DEAD10C5/badge-2017-bsidesindy/image/bsin.jpg

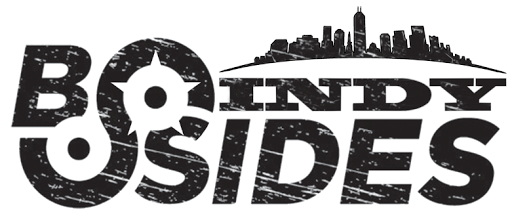
image/bsin.jpg
