DEAD10C5/badge-2017-bsidesindy/image/cleaver2.jpg

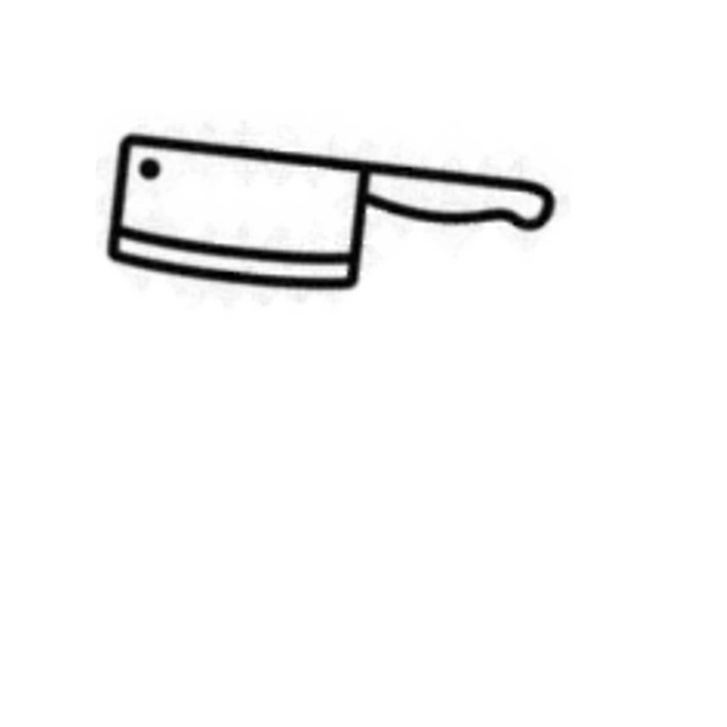
image/cleaver2.jpg
