DEAD10C5/badge-2017-bsidesindy/image/Screenshot-1 Board - -home-thedevilsvoice-eagle-tsrt-untitled.brd-EAGLE 7.5.0 Light.png

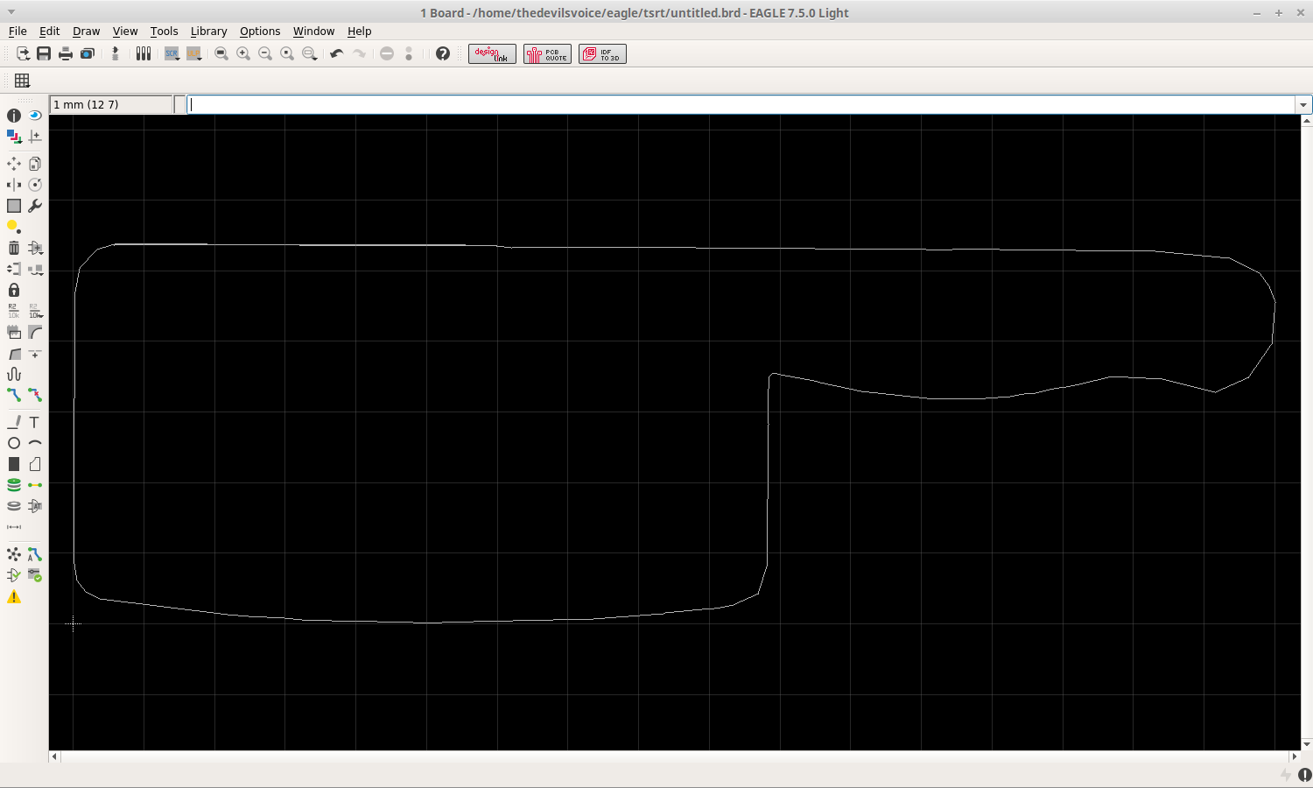
image/Screenshot-1 Board - -home-thedevilsvoice-eagle-tsrt-untitled.brd-EAGLE 7.5.0 Light.png
