DEAD10C5/badge-2017-bsidesindy/image/Screenshot-3.png

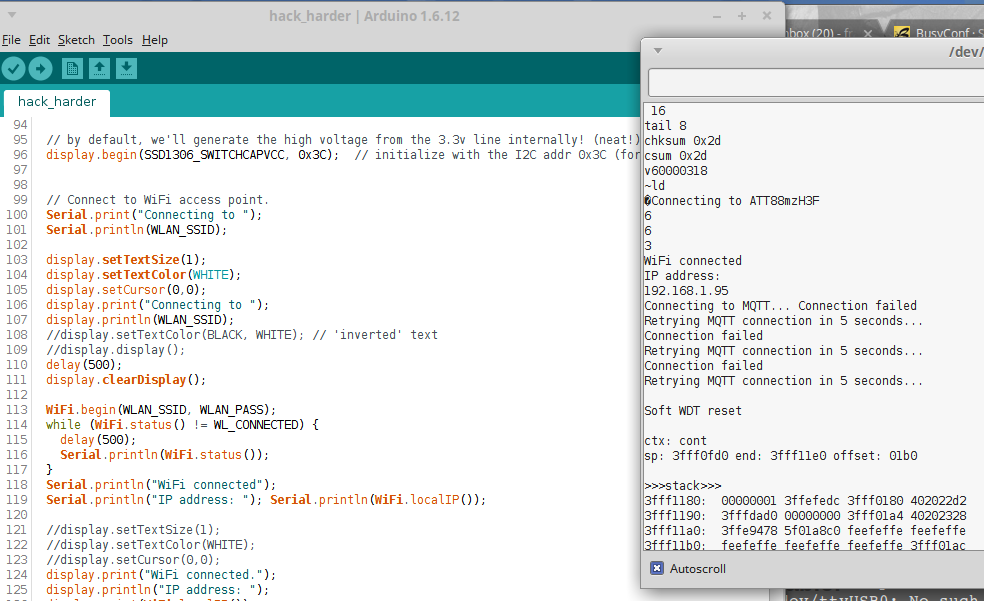
image/Screenshot-3.png
