DEAD10C5/badge-2017-bsidesindy/image/switch1.png

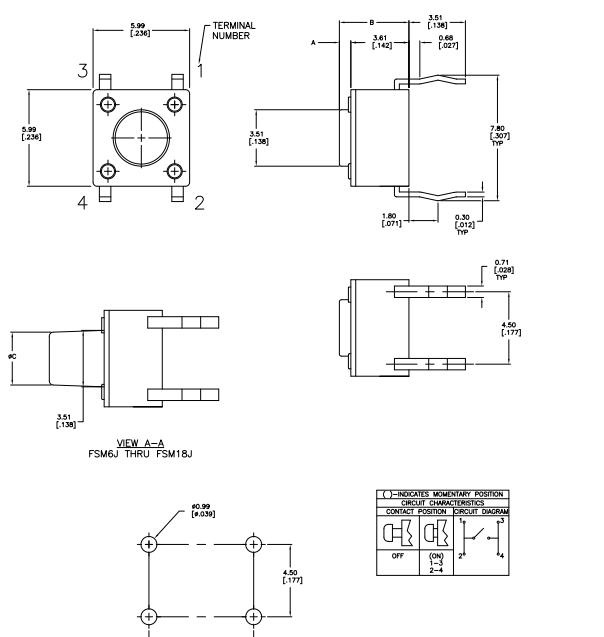
image/switch1.png
